SNESNESCUBE64/SpaceFirebirdSoundboard/Space Firebird Soundboard.sch

## KiCad design Space Firebird Soundboard.sch (2021-12-27)

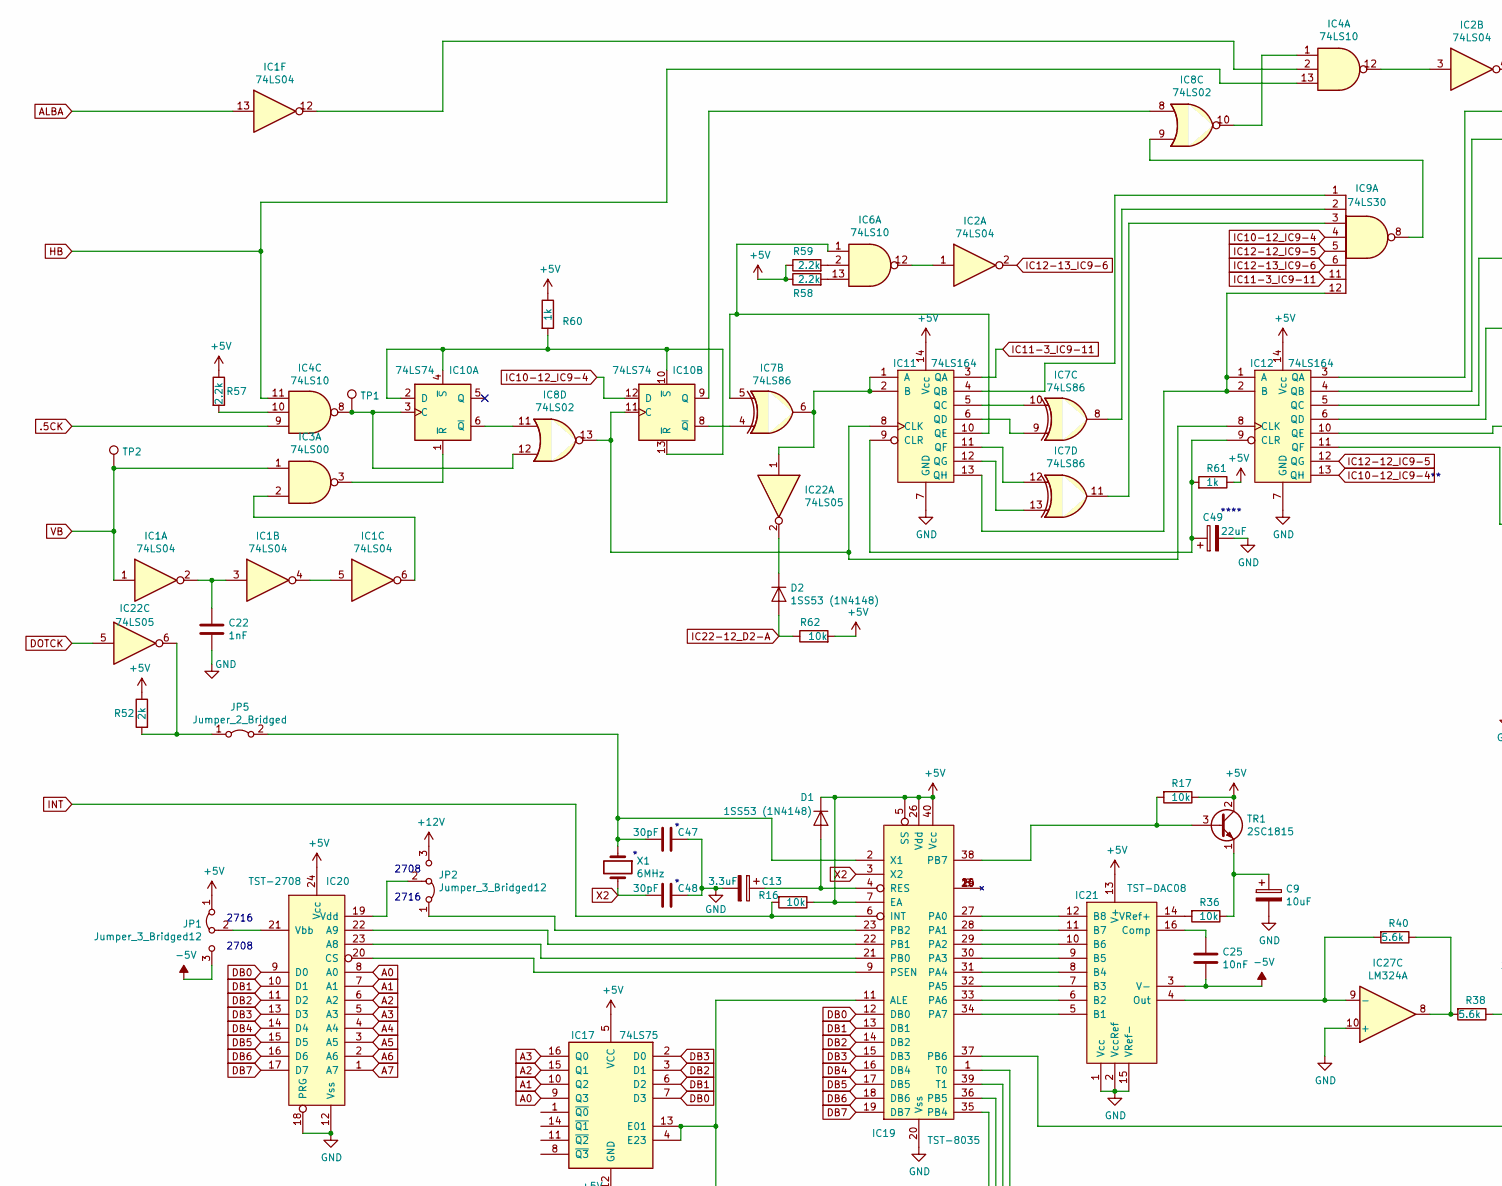
[picture p5: schematic Space Firebird Soundboard.sch, part in row 1, column 1]

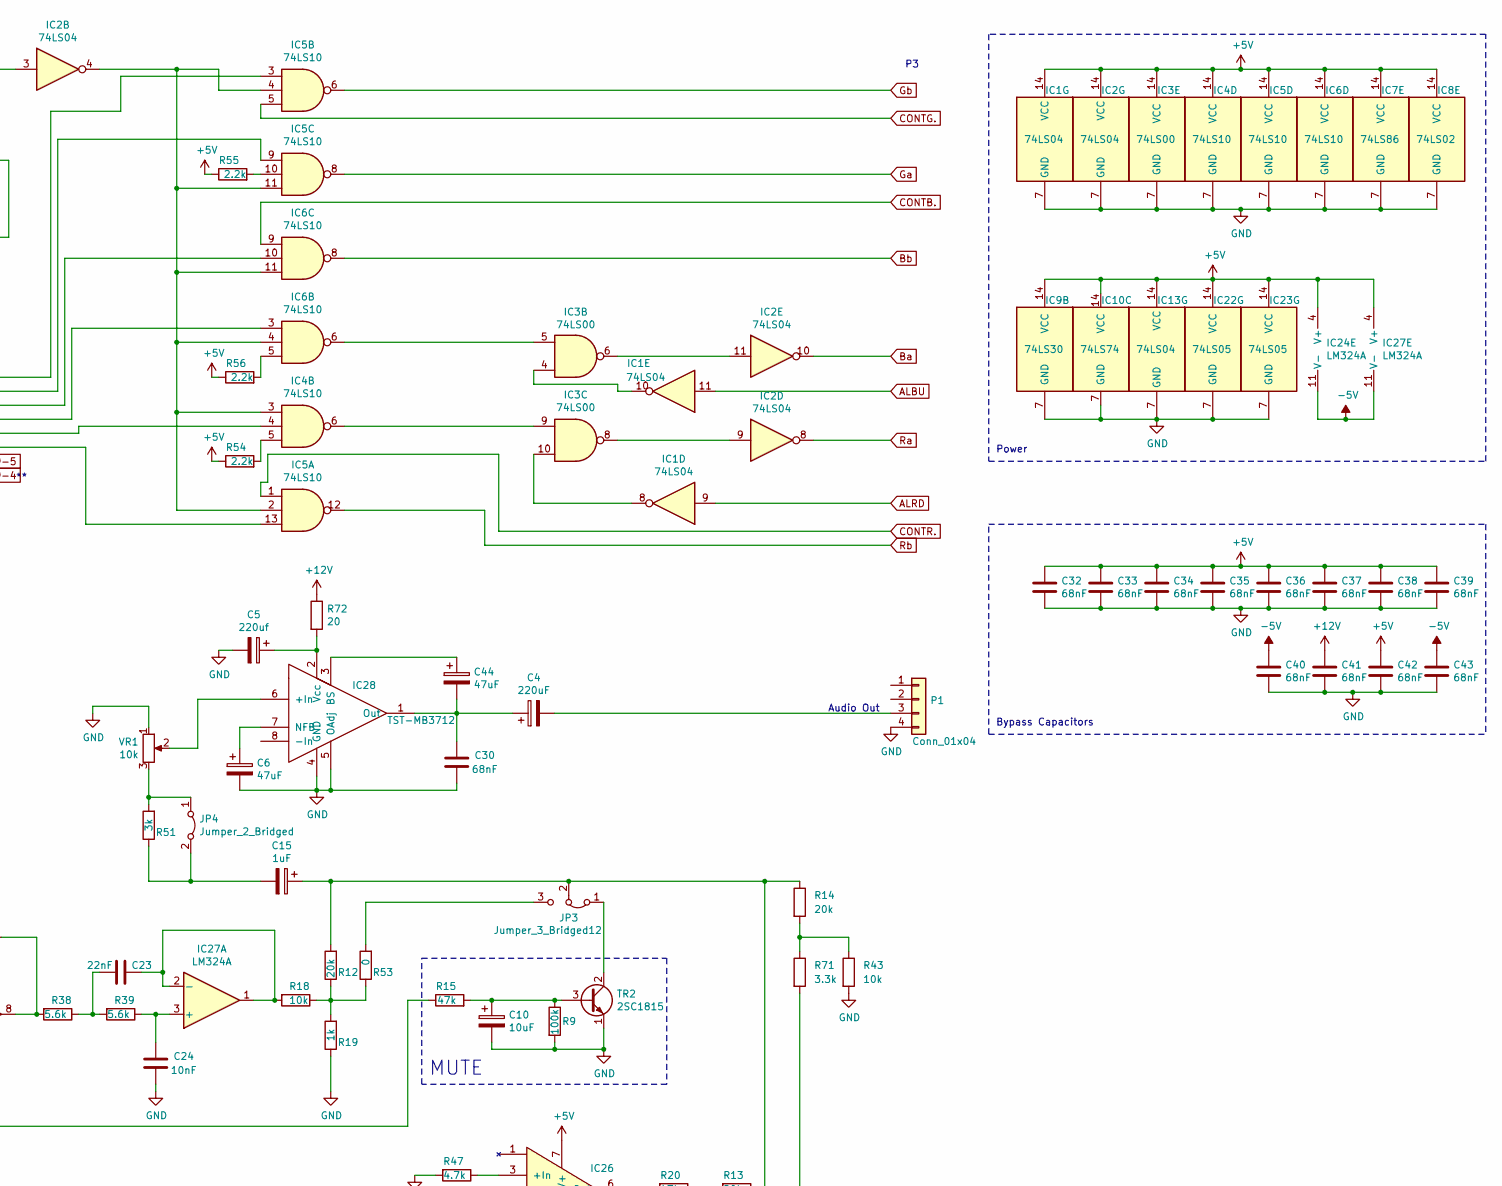
[picture p6: schematic Space Firebird Soundboard.sch, part in row 1, column 2]

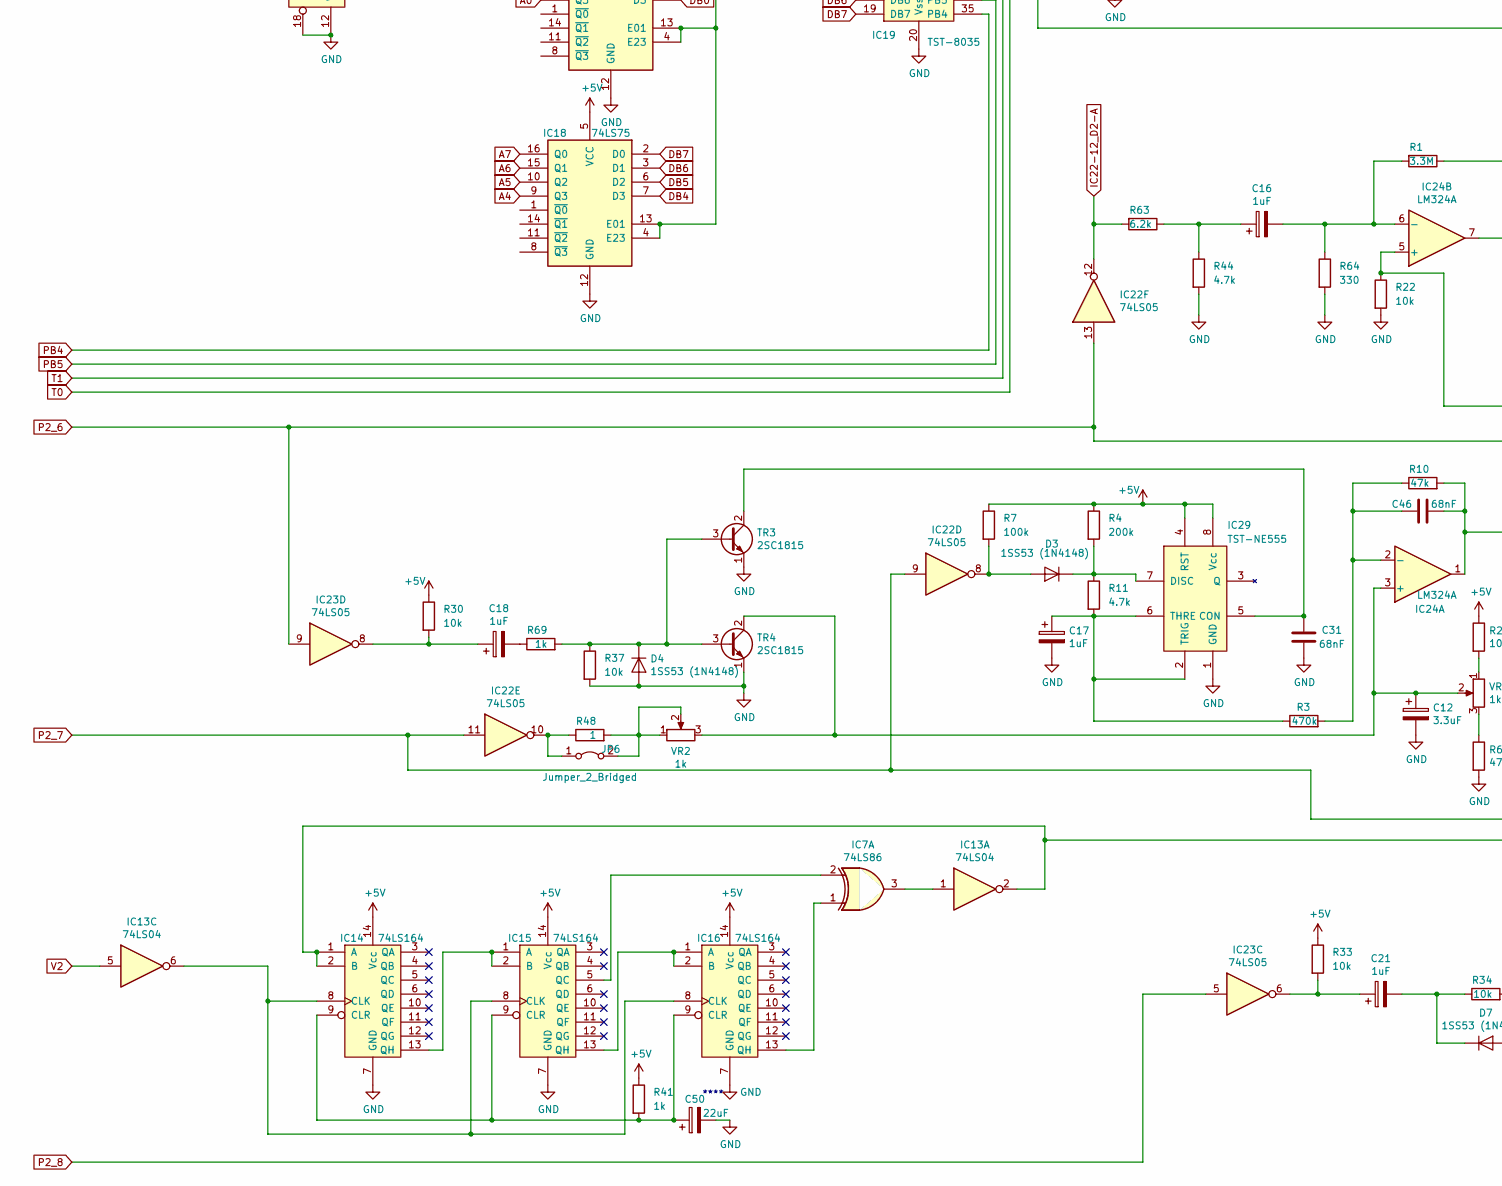
[picture p7: schematic Space Firebird Soundboard.sch, part in row 2, column 1]

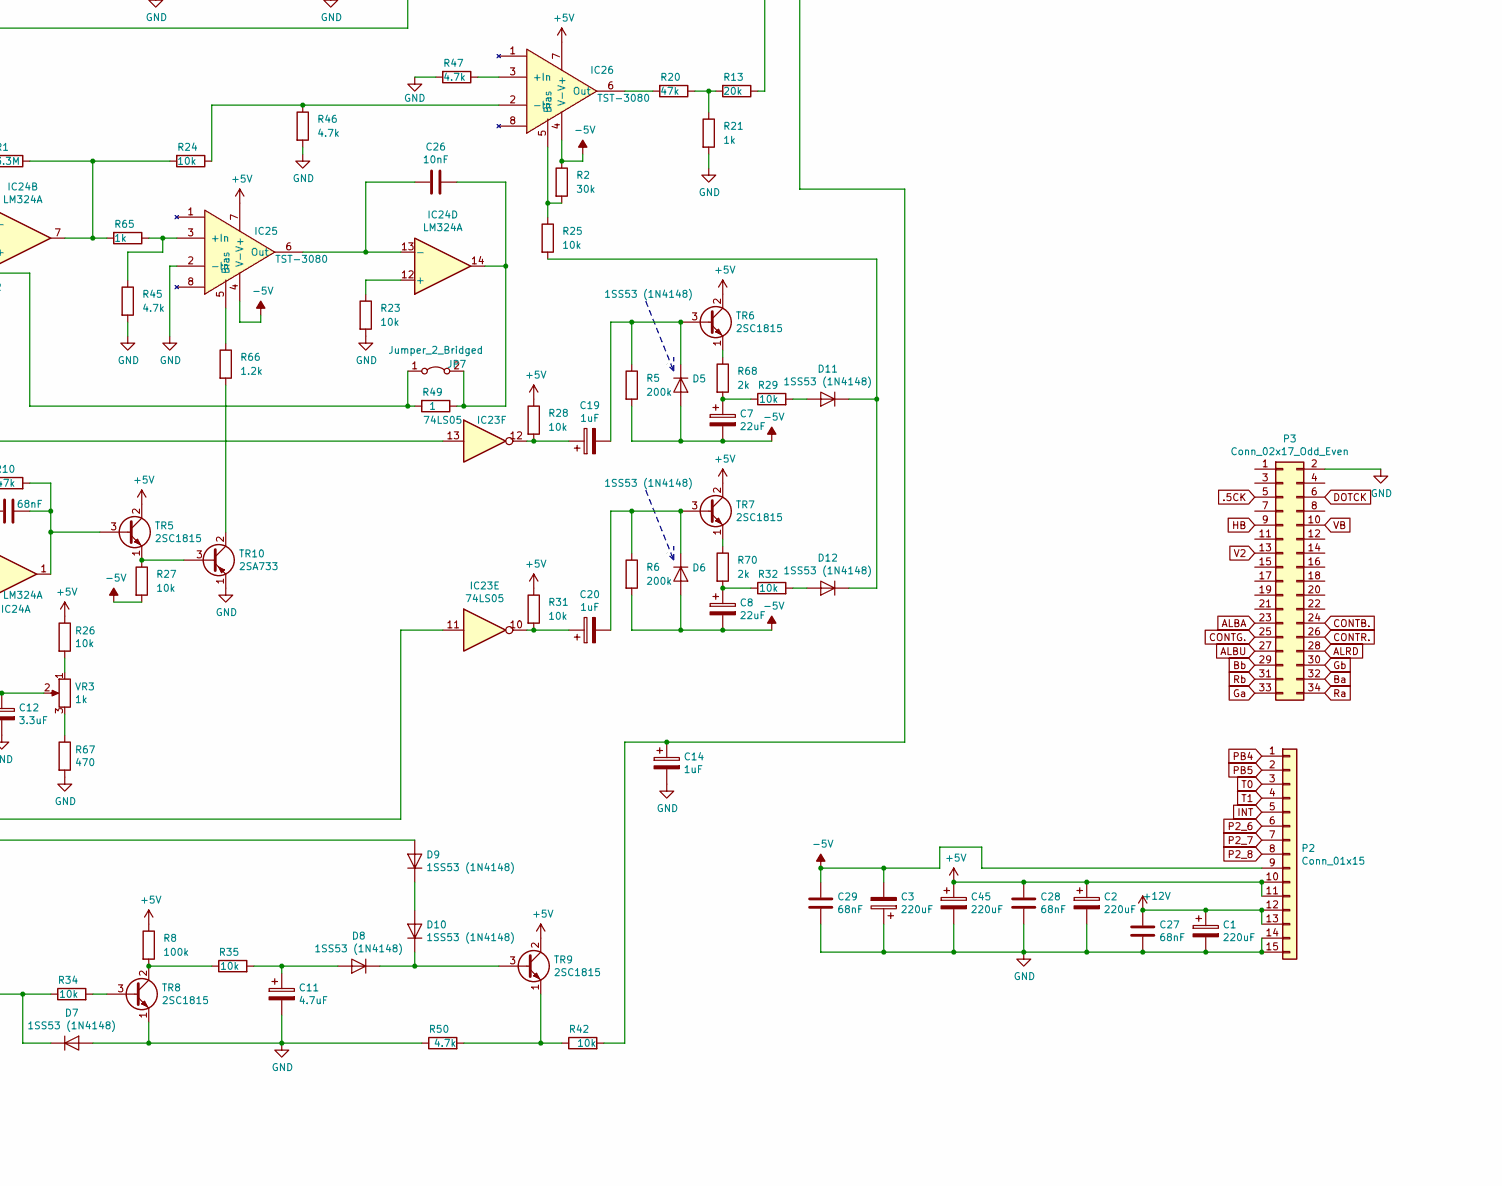
[picture p8: schematic Space Firebird Soundboard.sch, part in row 2, column 2]

Parts:
C1, C2, C3, C4, C45: 220uF; CP_Radial_D8.0mm_P3.80mm
C5: 220uf; CP_Radial_D8.0mm_P3.80mm
C6, C44: 47uF; CP_Radial_D6.3mm_P2.50mm
C7, C8, C49, C50: 22uF; CP_Radial_D5.0mm_P2.50mm
C9, C10: 10uF; CP_Radial_D5.0mm_P2.50mm
C11: 4.7uF; CP_Radial_D5.0mm_P2.50mm
C12, C13: 3.3uF; CP_Radial_D5.0mm_P2.50mm
C14, C15, C16, C17, C18, C19, C20, C21: 1uF; CP_Radial_D5.0mm_P2.50mm
C22: 1nF; C_Disc_D3.8mm_W2.6mm_P2.50mm
C23: 22nF; C_Disc_D3.8mm_W2.6mm_P2.50mm
C24, C25, C26: 10nF; C_Disc_D3.8mm_W2.6mm_P2.50mm
C27, C28, C29, C30, C31, C32, C33, C34, C35, C36, C37, C38, C39, C40, C41, C42, C43, C46: 68nF; C_Disc_D10.0mm_W2.5mm_P5.00mm
C47, C48: 30pF; C_Disc_D3.4mm_W2.1mm_P2.50mm
D1, D2, D3, D4, D5, D6, D7, D8, D9, D10, D11, D12: 1SS53 (1N4148); D_DO-35_SOD27_P12.70mm_Horizontal
IC1, IC2, IC13: 74LS04; DIP-14_W7.62mm
IC3: 74LS00; DIP-14_W7.62mm
IC4, IC5, IC6: 74LS10; DIP-14_W7.62mm
IC7: 74LS86; DIP-14_W7.62mm
IC8: 74LS02; DIP-14_W7.62mm
IC9: 74LS30; DIP-14_W7.62mm
IC10: 74LS74; DIP-14_W7.62mm
IC11, IC12, IC14, IC15, IC16: 74LS164; DIP-14_W7.62mm
IC17, IC18: 74LS75; DIP-16_W7.62mm
IC19: TST-8035; DIP-40_W15.24mm_Socket
IC20: TST-2708; DIP-24_W15.24mm_Socket
IC21: TST-DAC08; DIP-16_W7.62mm_Socket
IC22, IC23: 74LS05; DIP-14_W7.62mm
IC24, IC27: LM324A; DIP-14_W7.62mm_Socket
IC25, IC26: TST-3080; DIP-8_W7.62mm_Socket
IC28: TST-MB3712; MB3712
IC29: TST-NE555; DIP-8_W7.62mm
JP1, JP2, JP3: Jumper_3_Bridged12; SolderJumper-3_P1.3mm_Bridged12_RoundedPad1.0x1.5mm_NumberL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
JP4, JP5, JP6, JP7: Jumper_2_Bridged; SolderJumper-2_P1.3mm_Bridged_RoundedPad1.0x1.5mm
P1: Conn_01x04; Pin_Header_Straight_1x04_Pitch2.54mm
P2: Conn_01x15; Pin_Header_Straight_1x15_Pitch2.54mm
P3: Conn_02x17_Odd_Even; 34_right_angle_ribbon
R1: 3.3M; R_Axial_DIN0309_L7.0mm_D3.2mm_P12.70mm_Horizontal
R2: 30k; R_Axial_DIN0309_L7.0mm_D3.2mm_P12.70mm_Horizontal
R3: 470k; R_Axial_DIN0309_L7.0mm_D3.2mm_P12.70mm_Horizontal
R4, R5, R6: 200k; R_Axial_DIN0309_L7.0mm_D3.2mm_P12.70mm_Horizontal
R7, R8, R9: 100k; R_Axial_DIN0309_L7.0mm_D3.2mm_P12.70mm_Horizontal
R10, R15, R20: 47k; R_Axial_DIN0309_L7.0mm_D3.2mm_P12.70mm_Horizontal
R11, R44, R45, R46, R47, R50: 4.7k; R_Axial_DIN0309_L7.0mm_D3.2mm_P12.70mm_Horizontal
R12, R13, R14: 20k; R_Axial_DIN0309_L7.0mm_D3.2mm_P12.70mm_Horizontal
R16, R17, R18, R22, R23, R24, R25, R26, R27, R28, R29, R30, R31, R32, R33, R34, R35, R36, R37, R42, R43, R62: 10k; R_Axial_DIN0309_L7.0mm_D3.2mm_P12.70mm_Horizontal
R19, R21, R41, R60, R61, R65, R69: 1k; R_Axial_DIN0309_L7.0mm_D3.2mm_P12.70mm_Horizontal
R38, R39, R40: 5.6k; R_Axial_DIN0309_L7.0mm_D3.2mm_P12.70mm_Horizontal
R48, R49: 1; R_Axial_DIN0309_L7.0mm_D3.2mm_P12.70mm_Horizontal
R51: 3k; R_Axial_DIN0309_L7.0mm_D3.2mm_P12.70mm_Horizontal
R52, R68, R70: 2k; R_Axial_DIN0309_L7.0mm_D3.2mm_P12.70mm_Horizontal
R53: 0; R_Axial_DIN0309_L7.0mm_D3.2mm_P12.70mm_Horizontal
R54, R55, R56, R57, R58, R59: 2.2k; R_Axial_DIN0309_L7.0mm_D3.2mm_P12.70mm_Horizontal
R63: 6.2k; R_Axial_DIN0309_L7.0mm_D3.2mm_P12.70mm_Horizontal
R64: 330; R_Axial_DIN0309_L7.0mm_D3.2mm_P12.70mm_Horizontal
R66: 1.2k; R_Axial_DIN0309_L7.0mm_D3.2mm_P12.70mm_Horizontal
R67: 470; R_Axial_DIN0309_L7.0mm_D3.2mm_P12.70mm_Horizontal
R71: 3.3k; R_Axial_DIN0309_L7.0mm_D3.2mm_P12.70mm_Horizontal
R72: 20; R_Axial_DIN0309_L7.0mm_D3.2mm_P12.70mm_Horizontal
TP1, TP2: Pin_Header_Straight_1x01_Pitch2.54mm
TR1, TR2, TR3, TR4, TR5, TR6, TR7, TR8, TR9: 2SC1815; TO-92_Inline_Narrow_Oval
TR10: 2SA733; TO-92_Inline_Narrow_Oval
VR1: 10k; Potentiometer_Trimmer_Piher_PT-15v15_Horizontal_Px15.0mm_Py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
VR2, VR3: 1k; Potentiometer_Trimmer_Piher_PT-10v10_Horizontal_Px10.0mm_Py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
X1: 6MHz; Crystal_HC18-U_Vertical

Connections:
+5V: C2.1, C28.1, C32.1, C33.1, C34.1, C35.1, C36.1, C37.1, C38.1, C39.1, C42.1, C45.1, D1.1 (K), IC1.14 (VCC), IC2.14 (VCC), IC3.14 (VCC), IC4.14 (VCC), IC5.14 (VCC), IC6.14 (VCC), IC7.14 (VCC), IC8.14 (VCC), IC9.14 (VCC), IC10.14 (VCC), IC11.14 (Vcc), IC12.14 (Vcc), IC13.14 (VCC), IC14.14 (Vcc), IC15.14 (Vcc), IC16.14 (Vcc), IC17.5 (VCC), IC18.5 (VCC), IC19.5 (SS), IC19.7 (EA), IC19.26 (Vdd), IC19.40 (Vcc), IC20.24 (Vcc), IC21.13 (V+), IC22.14 (VCC), IC23.14 (VCC), IC24.4 (V+), IC25.7 (V+), IC26.7 (V+), IC27.4 (V+), IC29.4 (RST), IC29.8 (Vcc), JP1.1 (A), P2.10, P2.11, R4.1, R7.1, R8.1, R16.1, R17.1, R26.1, R28.1, R30.1, R31.1, R33.1, R41.1, R52.1, R54.1, R55.1, R56.1, R57.1, R58.1, R59.1, R60.1, R61.1, R62.2, TR1.2 (C), TR5.2 (C), TR6.2 (C), TR7.2 (C), TR9.2 (C)
+12V: C1.1, C27.1, C41.1, JP2.3 (B), P2.12, P2.13, R72.1
-5V: C3.2, C7.2, C8.2, C25.2, C29.1, C40.1, C43.1, D5.2 (A), D6.2 (A), IC21.3 (V-), IC24.11 (V-), IC25.4 (V-), IC26.4 (V-), IC27.11 (V-), JP1.3 (B), P2.9, R2.1, R5.2, R6.2, R27.2
.5CK: IC4.9, P3.5
A0: IC17.9 (Q3), IC20.8 (A0)
A1: IC17.10 (Q2), IC20.7 (A1)
A2: IC17.15 (Q1), IC20.6 (A2)
A3: IC17.16 (Q0), IC20.5 (A3)
A4: IC18.9 (Q3), IC20.4 (A4)
A5: IC18.10 (Q2), IC20.3 (A5)
A6: IC18.15 (Q1), IC20.2 (A6)
A7: IC18.16 (Q0), IC20.1 (A7)
ALBA: IC1.13, P3.23
ALBU: IC1.11, P3.27
ALRD: IC1.9, P3.28
Ba: IC2.10, P3.32
Bb: IC6.8, P3.29
CONTB.: IC6.9, P3.24
CONTG.: IC5.5, P3.25
CONTR.: IC5.1, P3.26
DB0: IC17.7 (D3), IC19.12 (DB0), IC20.9 (D0)
DB1: IC17.6 (D2), IC19.13 (DB1), IC20.10 (D1)
DB2: IC17.3 (D1), IC19.14 (DB2), IC20.11 (D2)
DB3: IC17.2 (D0), IC19.15 (DB3), IC20.13 (D3)
DB4: IC18.7 (D3), IC19.16 (DB4), IC20.14 (D4)
DB5: IC18.6 (D2), IC19.17 (DB5), IC20.15 (D5)
DB6: IC18.3 (D1), IC19.18 (DB6), IC20.16 (D6)
DB7: IC18.2 (D0), IC19.19 (DB7), IC20.17 (D7)
DOTCK: IC22.5, P3.6
GND: C1.2, C2.2, C3.1, C5.2, C6.2, C9.2, C10.2, C11.2, C12.2, C13.2, C14.2, C17.2, C22.2, C24.2, C27.2, C28.2, C29.2, C30.2, C31.2, C32.2, C33.2, C34.2, C35.2, C36.2, C37.2, C38.2, C39.2, C40.2, C41.2, C42.2, C43.2, C45.2, C47.1, C48.1, C49.2, C50.2, D4.2 (A), D7.2 (A), IC1.7 (GND), IC2.7 (GND), IC3.7 (GND), IC4.7 (GND), IC5.7 (GND), IC6.7 (GND), IC7.7 (GND), IC8.7 (GND), IC9.7 (GND), IC10.7 (GND), IC11.7 (GND), IC12.7 (GND), IC13.7 (GND), IC14.7 (GND), IC15.7 (GND), IC16.7 (GND), IC17.12 (GND), IC18.12 (GND), IC19.20 (Vss), IC20.12 (Vss), IC20.18 (PRG), IC21.1 (Vcc), IC21.2 (VccRef), IC21.15 (VRef-), IC22.7 (GND), IC23.7 (GND), IC25.2 (-In), IC27.10 (+), IC28.4 (GND), IC28.5 (OAdj), IC29.1 (GND), P1.4, P2.14, P2.15, P3.2, R9.2, R19.1, R21.2, R22.2, R23.2, R37.2, R43.2, R44.2, R45.2, R46.2, R47.2, R50.1, R64.2, R67.2, TR2.1 (E), TR3.1 (E), TR4.1 (E), TR8.1 (E), TR10.1 (E), VR1.1
Ga: IC5.8, P3.33
Gb: IC5.6, P3.30
HB: IC4.11, IC4.13, P3.9
IC10-12_IC9-4: IC9.4, IC10.12 (D), IC12.13 (QH)
IC11-3_IC9-11: IC9.11, IC11.3 (QA)
IC12-12_IC9-5: IC9.5, IC12.12 (QG)
IC12-13_IC9-6: IC2.2, IC9.6
IC22-12_D2-A: D2.2 (A), IC22.12, R62.1, R63.2
INT: IC19.6 (INT), P2.5, R16.2
unnamed: C4.2, P1.3
unnamed: C5.1, IC28.2 (Vcc), R72.2
unnamed: C6.1, IC28.7 (NFB)
unnamed: C7.1, R29.1, R68.2
unnamed: C8.1, R32.1, R70.2
unnamed: C9.1, R36.1, TR1.1 (E)
unnamed: C10.1, R9.1, R15.2, TR2.3 (B)
unnamed: C11.1, D8.2 (A), R35.2
unnamed: C12.1, IC24.3 (+), TR4.2 (C), VR2.3, VR3.2
unnamed: C13.1, D1.2 (A), IC19.4 (RES)
unnamed: C14.1, R42.2, R71.2
unnamed: C15.1, JP3.2 (C), R12.2, R13.1, R14.1
unnamed: C15.2, JP4.2 (B), R51.1
unnamed: C16.1, R44.1, R63.1
unnamed: C16.2, IC24.6 (-), R1.2, R64.1
unnamed: C17.1, IC29.2 (TRIG), IC29.6 (THRE), R3.1, R11.2
unnamed: C18.1, IC23.8, R30.2
unnamed: C18.2, R69.1
unnamed: C19.1, IC23.12, R28.2
unnamed: C19.2, D5.1 (K), R5.1, TR6.3 (B)
unnamed: C20.1, IC23.10, R31.2
unnamed: C20.2, D6.1 (K), R6.1, TR7.3 (B)
unnamed: C21.1, IC23.6, R33.2
unnamed: C21.2, D7.1 (K), R34.1
unnamed: C22.1, IC1.2, IC1.3
unnamed: C23.1, IC27.1, IC27.2 (-), R18.2
unnamed: C23.2, R38.1, R39.2
unnamed: C24.1, IC27.3 (+), R39.1
unnamed: C25.1, IC21.16 (Comp)
unnamed: C26.1, IC24.14, JP7.2 (B), R49.1
unnamed: C26.2, IC24.13 (-), IC25.6 (Out)
unnamed: C4.1, C30.1, C44.2, IC28.1 (Out)
unnamed: C31.1, IC29.5 (CON), TR3.2 (C)
unnamed: C44.1, IC28.3 (BS)
unnamed: C46.1, IC24.2 (-), R3.2, R10.1
unnamed: C46.2, IC24.1, R10.2, TR5.3 (B)
unnamed: C47.2, IC19.2 (X1), JP5.2 (B), X1.1
unnamed: C49.1, IC11.9 (CLR), IC12.9 (CLR), R61.2
unnamed: C50.1, IC14.9 (CLR), IC15.9 (CLR), IC16.9 (CLR), R41.2
unnamed: D2.1 (K), IC22.2
unnamed: D3.1 (K), IC29.7 (DISC), R4.2, R11.1
unnamed: D3.2 (A), IC22.8, R7.2
unnamed: D4.1 (K), R37.1, R69.2, TR3.3 (B), TR4.3 (B)
unnamed: D9.2 (A), IC13.2, IC14.1 (A), IC14.2 (B)
unnamed: D8.1 (K), D10.1 (K), TR9.3 (B)
unnamed: D9.1 (K), D10.2 (A)
unnamed: D11.1 (K), D12.1 (K), R25.2
unnamed: D11.2 (A), R29.2
unnamed: D12.2 (A), R32.2
unnamed: IC1.4, IC1.5
unnamed: IC1.6, IC3.2
unnamed: IC1.8, IC3.10
unnamed: IC1.10, IC3.4
unnamed: IC1.12, IC4.2
unnamed: IC2.1, IC6.12
unnamed: IC2.3, IC4.12
unnamed: IC2.4, IC4.3, IC5.2, IC5.4, IC5.11, IC6.4, IC6.11
unnamed: IC2.9, IC3.8
unnamed: IC2.11, IC3.6
unnamed: IC3.5, IC6.6
unnamed: IC3.9, IC4.6
unnamed: IC4.1, IC8.10
unnamed: IC4.5, R54.2
unnamed: IC4.10, R57.2
unnamed: IC5.10, R55.2
unnamed: IC6.2, R59.2
unnamed: IC6.5, R56.2
unnamed: IC6.13, R58.2
unnamed: IC7.8, IC9.2
unnamed: IC7.11, IC9.3
unnamed: IC8.9, IC9.8
unnamed: IC3.3, IC10.1 (~R)
unnamed: IC4.8, IC8.12, IC10.3 (C), TP1.1
unnamed: IC8.11, IC10.6 (~Q)
unnamed: IC7.4, IC10.8 (~Q)
unnamed: IC8.8, IC10.9 (Q)
unnamed: IC10.2 (D), IC10.4 (~S), IC10.10 (~S), IC10.13 (~R), R60.2
unnamed: IC8.13, IC10.11 (C), IC11.8 (CLK), IC12.8 (CLK)
unnamed: IC7.6, IC11.1 (A), IC11.2 (B), IC22.1
unnamed: IC9.1, IC11.4 (QB)
unnamed: IC7.10, IC11.5 (QC)
unnamed: IC7.9, IC11.6 (QD)
unnamed: IC6.1, IC7.5, IC11.10 (QE)
unnamed: IC7.12, IC11.11 (QF)
unnamed: IC7.13, IC11.12 (QG)
unnamed: IC9.12, IC11.13 (QH), IC12.1 (A), IC12.2 (B)
unnamed: IC5.3, IC12.3 (QA)
unnamed: IC5.9, IC12.4 (QB)
unnamed: IC6.10, IC12.5 (QC)
unnamed: IC6.3, IC12.6 (QD)
unnamed: IC4.4, IC12.10 (QE)
unnamed: IC5.13, IC12.11 (QF)
unnamed: IC7.3, IC13.1
unnamed: IC13.6, IC14.8 (CLK), IC15.8 (CLK), IC16.8 (CLK)
unnamed: IC14.13 (QH), IC15.1 (A), IC15.2 (B)
unnamed: IC7.2, IC15.5 (QC)
unnamed: IC15.13 (QH), IC16.1 (A), IC16.2 (B)
unnamed: IC7.1, IC16.13 (QH)
unnamed: IC17.4 (E23), IC17.13 (E01), IC18.4 (E23), IC18.13 (E01), IC19.11 (ALE)
unnamed: IC19.9 (PSEN), IC20.20 (CS)
unnamed: IC19.8, IC19.10, IC19.24, IC19.25
unnamed: IC19.21 (PB0), IC20.23 (A8)
unnamed: IC19.22 (PB1), IC20.22 (A9)
unnamed: IC19.23 (PB2), JP2.1 (A)
unnamed: IC19.27 (PA0), IC21.12 (B8)
unnamed: IC19.28 (PA1), IC21.11 (B7)
unnamed: IC19.29 (PA2), IC21.10 (B6)
unnamed: IC19.30 (PA3), IC21.9 (B5)
unnamed: IC19.31 (PA4), IC21.8 (B4)
unnamed: IC19.32 (PA5), IC21.7 (B3)
unnamed: IC19.33 (PA6), IC21.6 (B2)
unnamed: IC19.34 (PA7), IC21.5 (B1)
unnamed: IC19.37 (PB6), R15.1
unnamed: IC19.38 (PB7), R17.2, TR1.3 (B)
unnamed: IC20.19 (Vdd), JP2.2 (C)
unnamed: IC20.21 (Vbb), JP1.2 (C)
unnamed: IC21.4 (Out), IC27.9 (-), R40.2
unnamed: IC21.14 (VRef+), R36.2
unnamed: IC22.6, JP5.1 (A), R52.2
unnamed: IC22.10, JP6.1 (A), R48.1
unnamed: IC24.5 (+), JP7.1 (A), R22.1, R49.2
unnamed: IC24.7, R1.1, R24.2, R65.2
unnamed: IC24.12 (+), R23.1
unnamed: IC25.3 (+In), R45.1, R65.1
unnamed: IC25.5 (Bias), R66.1
unnamed: IC26.2 (-In), R24.1, R46.1
unnamed: IC26.3 (+In), R47.1
unnamed: IC26.5 (Bias), R2.2, R25.1
unnamed: IC26.6 (Out), R20.2
unnamed: IC27.8, R38.2, R40.1
unnamed: IC28.6 (+In), VR1.2
unnamed: JP3.1 (A), TR2.2 (C)
unnamed: JP3.3 (B), R53.2
unnamed: JP4.1 (A), R51.2, VR1.3
unnamed: JP6.2 (B), R48.2, VR2.1, VR2.2
unnamed: R12.1, R18.1, R19.2, R53.1
unnamed: R13.2, R20.1, R21.1
unnamed: R14.2, R43.1, R71.1
unnamed: R26.2, VR3.1
unnamed: R27.1, TR5.1 (E), TR10.3 (B)
unnamed: R34.2, TR8.3 (B)
unnamed: R8.2, R35.1, TR8.2 (C)
unnamed: R42.1, R50.2, TR9.1 (E)
unnamed: R66.2, TR10.2 (C)
unnamed: R67.1, VR3.3
unnamed: R68.1, TR6.1 (E)
unnamed: R70.1, TR7.1 (E)
P2_6: IC22.13, IC23.9, IC23.13, P2.6
P2_7: IC22.9, IC22.11, IC23.11, P2.7
P2_8: IC23.5, P2.8
PB4: IC19.35 (PB4), P2.1
PB5: IC19.36 (PB5), P2.2
Ra: IC2.8, P3.34
Rb: IC5.12, P3.31
T0: IC19.1 (T0), P2.3
T1: IC19.39 (T1), P2.4
V2: IC13.5, P3.13
VB: IC1.1, IC3.1, P3.10, TP2.1
X2: C48.2, IC19.3 (X2), X1.2

Notes on the sheet:
2708
2716
MUTE
Audio Out
Power
Bypass Capacitors
****
